ak66666/ThumbsUpV3Rp2040/Photos/IMG_20240202_221632282.jpg

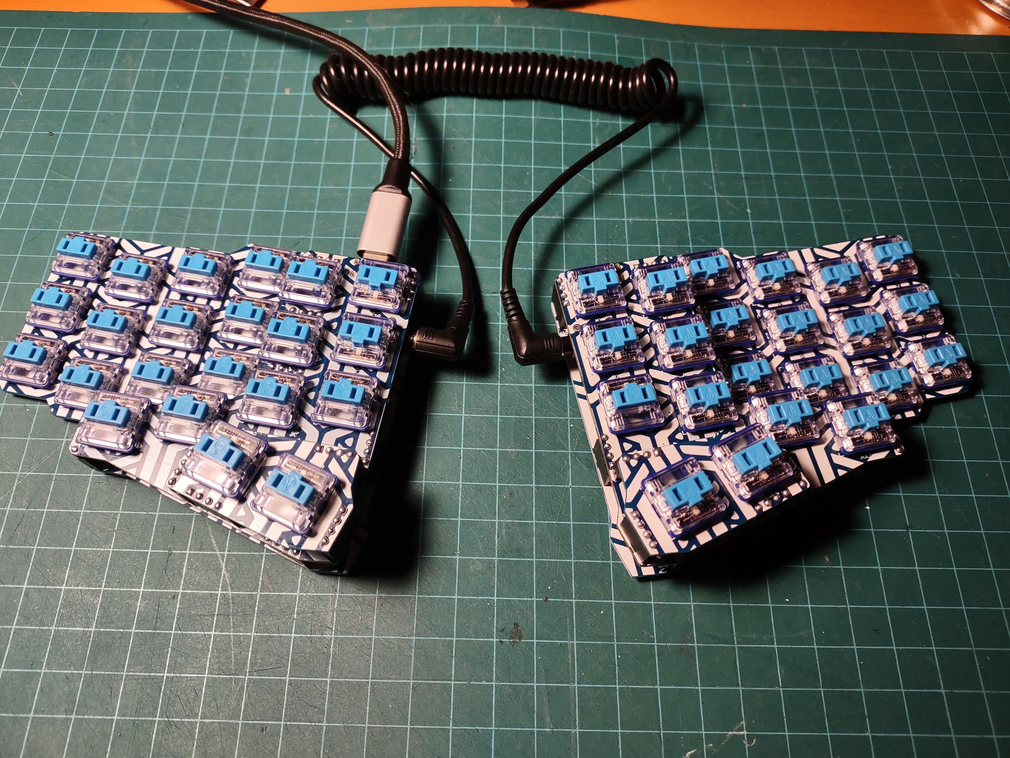
Photos/IMG_20240202_221632282.jpg
