ak66666/ThumbsUpV3Rp2040/Photos/IMG_20240202_221721445_HDR.jpg

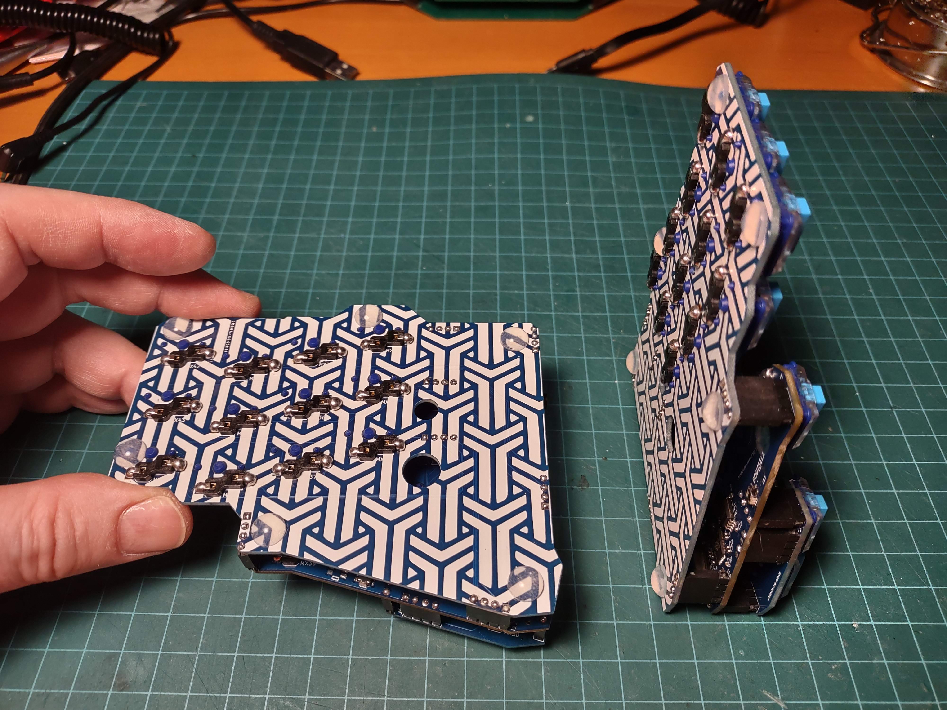
Photos/IMG_20240202_221721445_HDR.jpg
