ak66666/ThumbsUpV3Rp2040/Silkscreens/Pattern.png

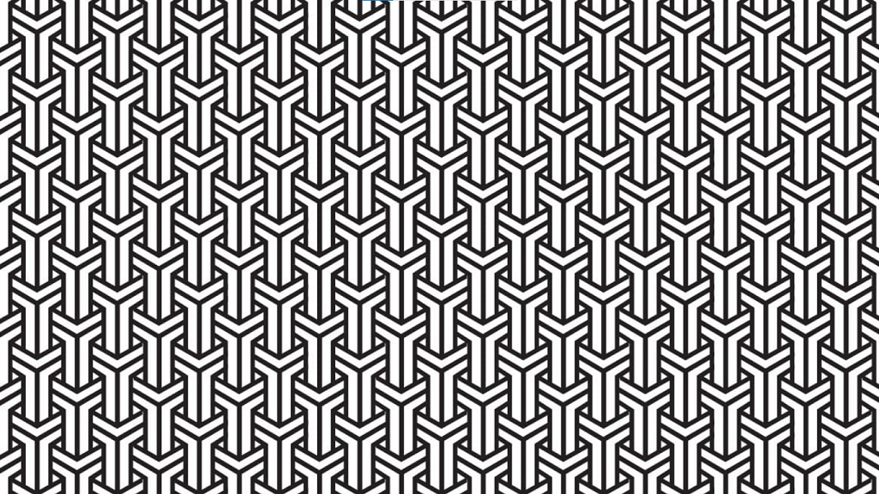
Silkscreens/Pattern.png
