ak66666/ThumbsUpV3Rp2040/Silkscreens/QWERTY.png

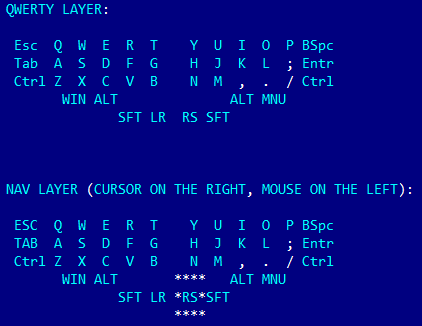
Silkscreens/QWERTY.png
